ucsbieee/Tesla-Coil-MIDI-Synth/Tesla_Coil_MIDI_Synth/AudioModeBinaryOctave.h

#pragma once

#include "AudioMode.h"

class AudioModeBinaryOctave: public AudioMode {
public:
  using AudioMode::AudioMode;

  virtual void reset() override;
  virtual uint16_t processSample(int32_t in) override;

  virtual const char *name() const override;

private:
  uint16_t pulseWidthCount = 0;
  bool state = false;
  bool lastState = false;
  bool octaveDown = false;
};
