ucsbieee/Tesla-Coil-MIDI-Synth/Tesla_Coil_MIDI_Synth/Synth.h

#pragma once

#include <inttypes.h>

// Uncomment to automatically reduce pulse width when many voices are playing at once
//#define AUTODUCK

// Uncomment to make MIDI velocity control absolute pulse width instead of duty cycle
//#define ABSOLUTE_PULSE_WIDTH

#define EXP_CRUNCH 3

#define MAX_WIDTH (3e-3f) // 3ms
#define MIN_WIDTH (10e-6f) // 10us
#define MIN_OFF_TIME (50e-6f) // 50us

#define MAX_WIDTH_CYC ((uint32_t)(F_CPU/2*MAX_WIDTH)) // max pulse width
#define MIN_WIDTH_CYC ((uint32_t)(F_CPU/2*MIN_WIDTH))  // min pulse width
#define MIN_OFF_TIME_CYC ((int32_t)(F_CPU/2*MIN_OFF_TIME)) // minimum time between pulses on each channel

#define VEL_THRESH 1 // minimum velocity
#define MAX_FREQ 4000 // if frequency is too high, pulses just merge together

#define DEFAULT_VOL 64

#define LUTSIZE 256

class Voices;
class MIDI;

class Synth {
public:
  Synth(Voices &voices, MIDI &midi);
  
  uint8_t vol = DEFAULT_VOL;
  
  // Functions
  void stop();
  void update();
  
private:
  Voices &voices;
  MIDI &midi;
  
  static uint8_t eLookup[LUTSIZE];
  static int8_t sinLookup[LUTSIZE];
  
  void updateWidth(uint8_t chan, uint32_t pulseWidth);
  void updatePeriod(uint8_t chan, uint32_t period);
};
